roman-dvorak/AIRDOS04/hw/cad/printplate_button.scad

use<pcb_rails.scad>;

for(x=[5, -5], y=[-4, 4, 10, -10]) translate([x, y, 0]) button();
