roman-dvorak/AIRDOS04/hw/cad/printplate_front_cover.scad

use<pcb_rails.scad>;

front_cover();
