roman-dvorak/AIRDOS04/hw/cad/printplate_pcbedge.scad

use<pcb_rails.scad>;

pcb_edge();
translate([0, 6, 0]) pcb_edge();
