roman-dvorak/AIRDOS04/hw/cad/printplate_rear_cover.scad

use<pcb_rails.scad>;

rear_cover();
