roman-dvorak/AIRDOS04/hw/cad/projection_front_cover.scad

use<pcb_rails.scad>;

projection(cut=true)
{
rotate([180, 0, 0]) translate([0, 0, 1.6]) front_cover();
}
