roman-dvorak/AIRDOS04/fw/AIRDOS04/githash.h

// This file is overwritten by github actions, do not update it manually
String githash = "059105d0adb1b8706a2c93dfa1840c3a36f70ef4,User";
#define GHRELEASE 1
#define GHBUILD 0
#define GHBUILDTYPE User
