roman-dvorak/AIRDOS04/fw/PROTOTYPE3/githash.h

// This file is overwritten by github actions, do not update it manually
String githash = "c70ff94987d7dd95c620b8e2d6ba4711ff3b70f4,User";
#define GHRELEASE 0
#define GHBUILD 0
#define GHBUILDTYPE User
